MushuDG/ATMegaSpin/3DModel/Parts/STA_CF18_STP.step

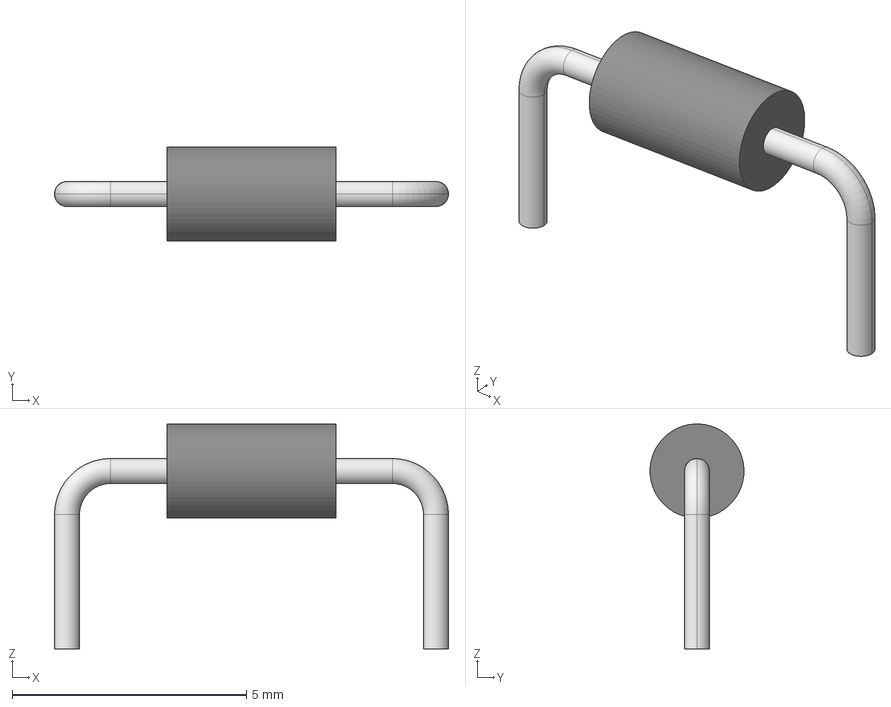
[picture p20: CAD file, 2023-11-16]
3DModel/Parts/STA_CF18_STP.step
8.41 x 2.01 x 4.80 mm
