MushuDG/ATMegaSpin/3DModel/Parts/ECS-160-18-4X-CKM.step

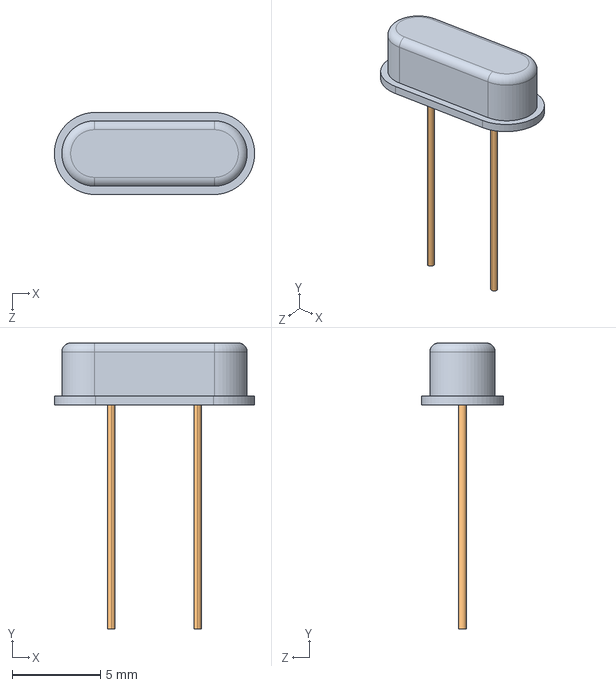
[picture p21: CAD file, 2023-11-15]
3DModel/Parts/ECS-160-18-4X-CKM.step
11.4 x 16.2 x 4.65 mm
