MushuDG/ATMegaSpin/3DModel/Parts/ED281DT.step

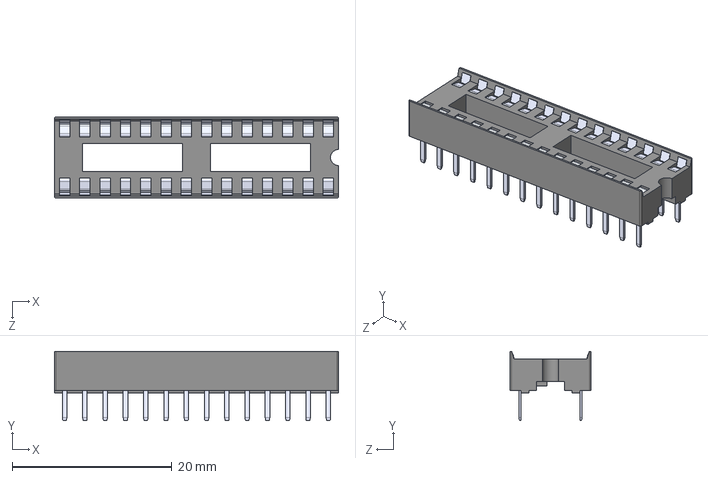
[picture p22: CAD file, 2023-11-14]
3DModel/Parts/ED281DT.step
35.6 x 8.70 x 10.2 mm
