MushuDG/ATMegaSpin/Inventor/button v2.stl

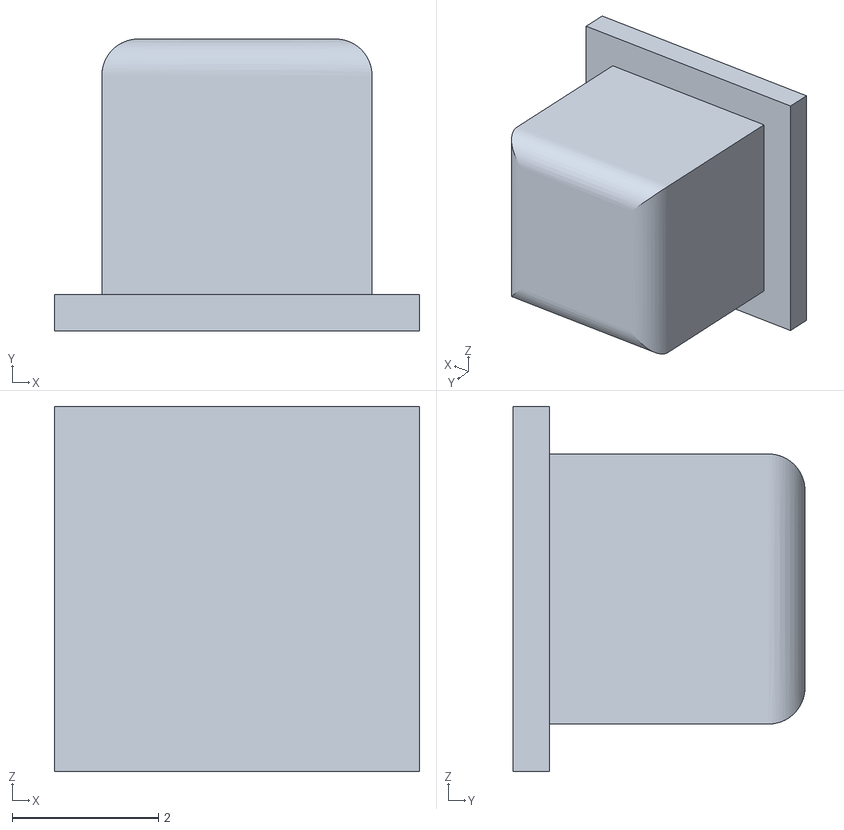
[picture p23: CAD file, 2023-12-23, an earlier design]
Inventor/button v2.stl
5.00 x 4.00 x 5.00
